Mustafa0801/LFR-thirdspace/CAD files/Fused Motor.FCStd

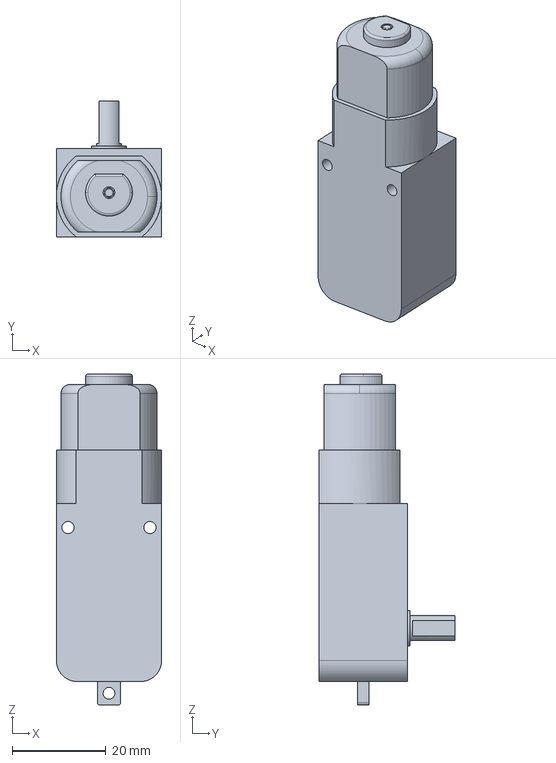
[picture p14: CAD file, 2026-09-21]
CAD files/Fused Motor.FCStd
22.5 x 29.0 x 70.7 mm
