Mustafa0801/LFR-thirdspace/final ship/chassis build current.FCStd

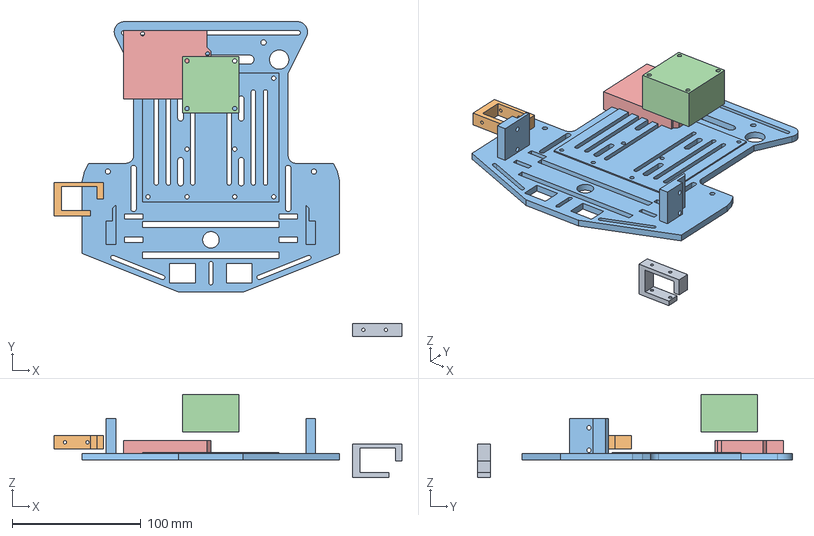
[picture p15: CAD file, 2026-10-05]
final ship/chassis build current.FCStd
270.1 x 244.4 x 64.4 mm
Bracket1
Bracket2
Base Chassis
L298n
Arduino
L298n001
