Mustafa0801/LFR-thirdspace/CAD files/Assorted Assets (Copy 3).FCStd

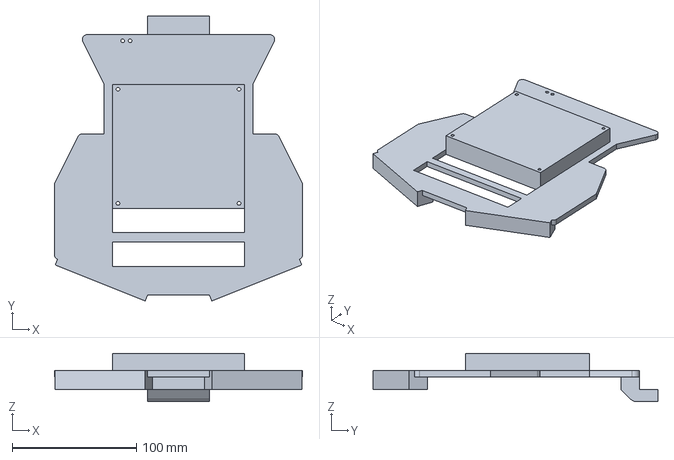
[picture p16: CAD file, 2026-09-21]
CAD files/Assorted Assets (Copy 3).FCStd
200.0 x 229.6 x 39.0 mm
