Mustafa0801/LFR-thirdspace/final ship/chassis build october 3 first space-saving cut.FCStd

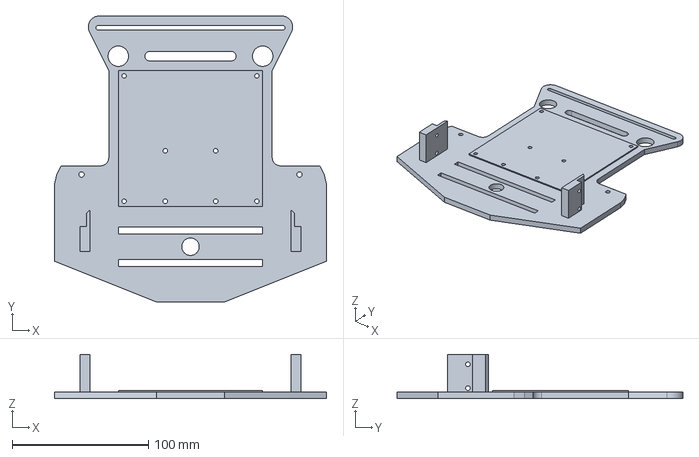
[picture p17: CAD file, 2026-10-05]
final ship/chassis build october 3 first space-saving cut.FCStd
200.0 x 210.0 x 32.5 mm
