Mustafa0801/LFR-thirdspace/CAD files/mule.FCStd

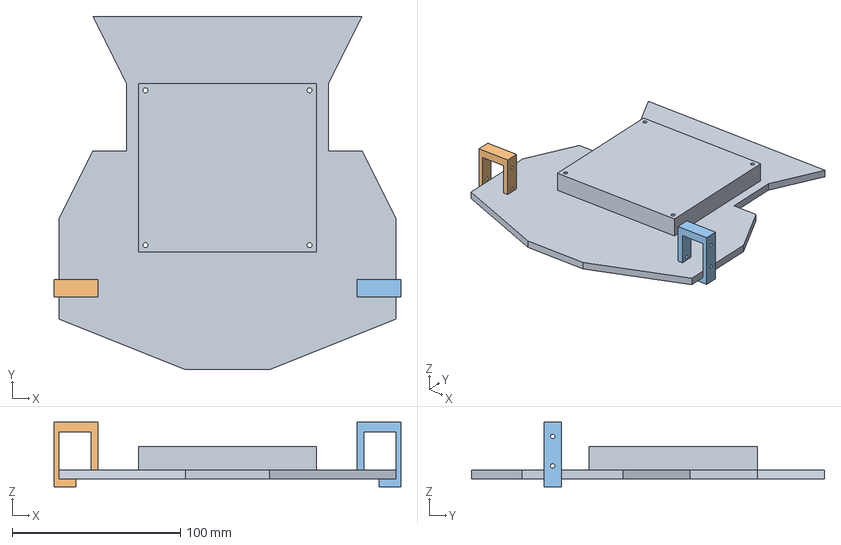
[picture p18: CAD file, 2026-09-21]
CAD files/mule.FCStd
206.2 x 210.0 x 38.5 mm
Base Chassis
Bracket2
Bracket1
