Mustafa0801/LFR-thirdspace/final ship/chassis build october 3 with proper sensor mount and hole for cables.FCStd

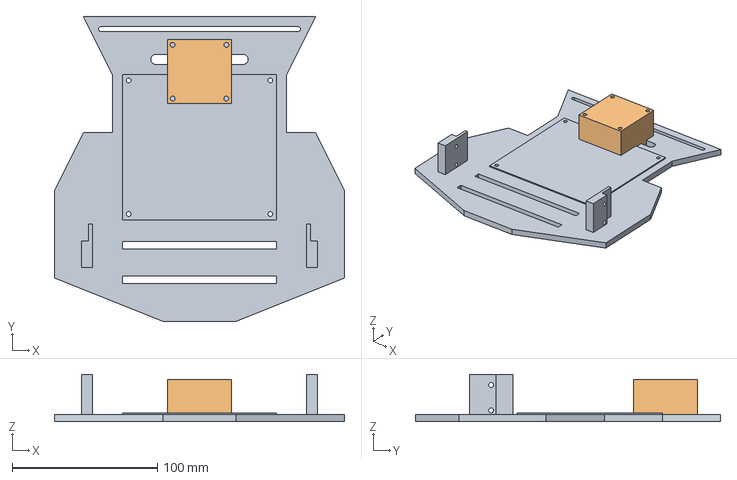
[picture p19: CAD file, 2026-10-05]
final ship/chassis build october 3 with proper sensor mount and hole for cables.FCStd
200.0 x 210.0 x 32.5 mm
Base Chassis
L298n
