Mustafa0801/LFR-thirdspace/CAD files/Assorted Assets (Copy).FCStd

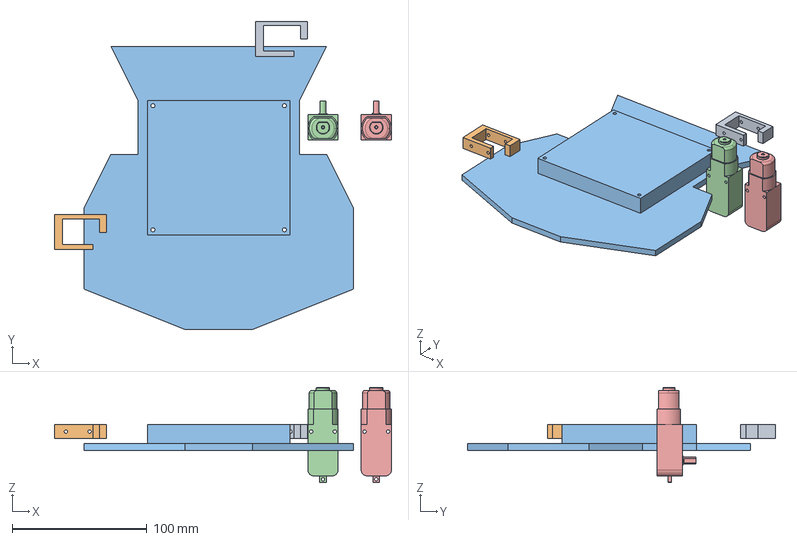
[picture p20: CAD file, 2026-09-21]
CAD files/Assorted Assets (Copy).FCStd
250.0 x 228.5 x 70.7 mm
Bracket1
Bracket2
Base Chassis
Motor fused1
MotorFused2
