Mustafa0801/LFR-thirdspace/CAD files/sensor hanging mounting bracket.FCStd

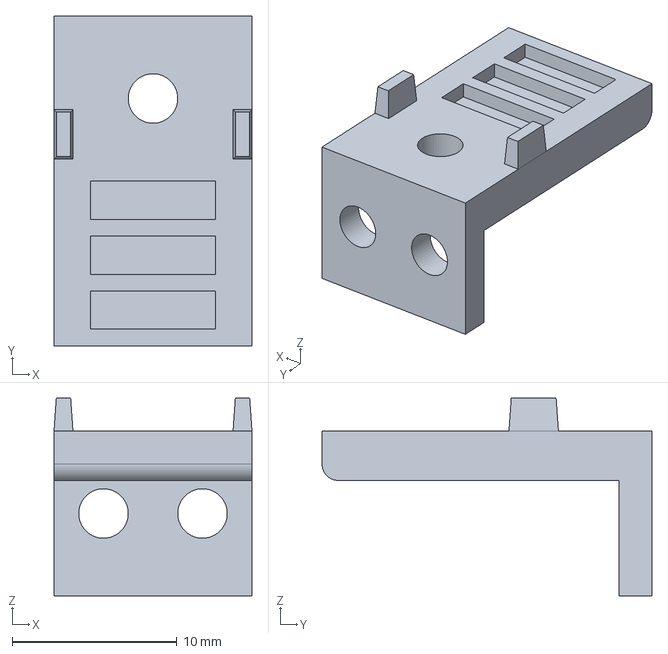
[picture p21: CAD file, 2026-09-21]
CAD files/sensor hanging mounting bracket.FCStd
12.0 x 20.0 x 12.0 mm
