Mustafa0801/LFR-thirdspace/CAD files/fusion1.FCStd

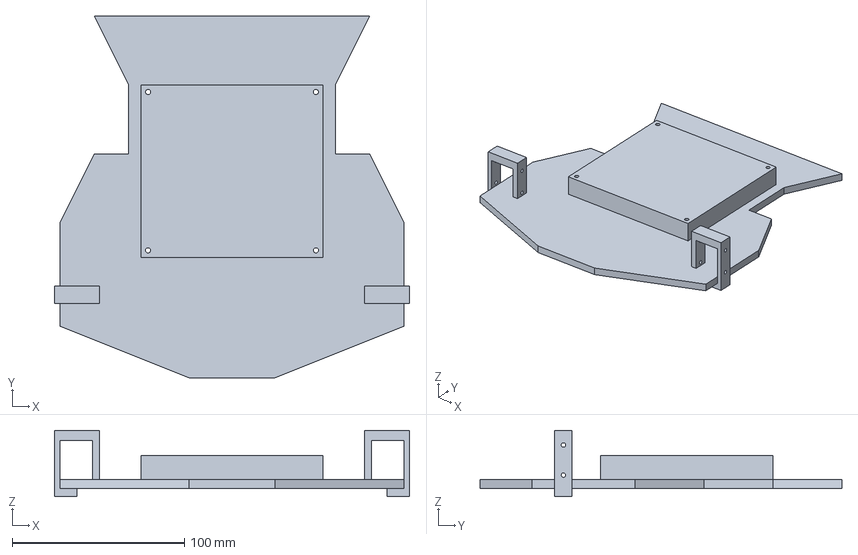
[picture p22: CAD file, 2026-09-21]
CAD files/fusion1.FCStd
206.2 x 210.0 x 38.5 mm
