Mustafa0801/LFR-thirdspace/CAD files/Assorted fusion.FCStd

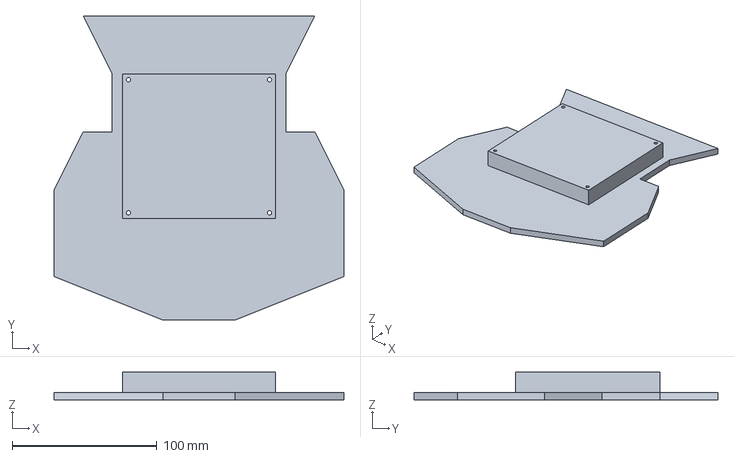
[picture p23: CAD file, 2026-09-21]
CAD files/Assorted fusion.FCStd
200.0 x 210.0 x 19.3 mm
