Mustafa0801/LFR-thirdspace/Arduino Code/other-ideas/speed-adjustment.ino

//  TEST/IDEA FOR HOW SPEED COULD AUTO ADJUST (FOR SHARP TURNS AND STUFF)

//  The code involves checking if a sensor has remained 0 consecutively, 
//  if this sensor is one of the left or right ones then that means a sharp turn is there so robot should slow down to allow it to follow the line properly
//  otherwise if it is the middle one we can deduce that it is following a straight line so it can speed up
// number of consecutive readings would need to be adjusted according to tests

int speed = 150;  // normal speed of car
int linePos;

int countL2 = 0;
int countL1 = 0;
int countM = 0;  // counts how many times each sensor has had value 0 consecutively
int countR1 = 0;
int countR2 = 0;
int consecutive = 2;  // this variable stores the number of consecutive times reading should be same for the robot to change speed (stored in variable to easily change later after tests) 

void setup() {
  // pin modes of sensors and motors here
  Serial.begin(9600);
}

void loop() {
  // ReadSensors function here which will return value for linePos
  
    // PLACEHOLDER: for now using random numbers for linePos
  int zeroChance = random(0,3);  // 33.33% chance the position is 0, this could more accurately represent how our readings probably will actually be with the full robot built 
  if (zeroChance == 0){          
    linePos = 0;
  }
  else{
    linePos = 2*(random(-2,3));  // since just using one random generator will have equal chance for each number
  }

  Serial.print(String(linePos)+"  ");

  switch (linePos){
    case -4:
      // turn left on point function 
      countL2 = countL2 + 1;  // increments counter for left most sensor
      countR2 = countR1 = countM = countL1 = 0;   // sets other counters to zero (since this means the other sensors havent had a consecutive same value)
      break;
    case -2:
      // move left function here
      countL1 = countL1 + 1;
      countR2 = countR1 = countM = countL2 = 0;
      break;
    case 0:
      // move forward function here
      countM = countM + 1;
      countR2 = countR1 = countL1 = countL2 = 0;
      break;
    case 2:
      // move right function here
      countR1 = countR1 + 1;
      countR2 = countM = countL1 = countL2 = 0;
      break;
    case 4:
      // turn right on point function here
      countR2 = countR2 + 1;
      countR1 = countM = countL1 = countL2 = 0;
      break;
  }

  if (countL2 == consecutive){
    if (speed>30){    // only decreases speed if above lower threshold of 30
      speed = speed*0.75;  // decreases speed by 25% 
      countL2 = 0;  // resets counter
      if (speed<30){  // if speed goes below 30 it is reset to 30
        speed = 30;
      }
      Serial.print("speed decreased to: "+String(speed));
    }
  } 
  else if (countL1 == consecutive){
    if (speed>50){     // only decreases speed if above 50
      speed = speed*0.9;  // decreases speed by 10%
      countL1 = 0;
      if (speed<50){  // if speed goes below 50 it is reset to 50
        speed = 50;
      }
      Serial.print("speed decreased to: "+String(speed));
    } 
  }
  else if (countM == consecutive){
    if (speed<150){   // only increases if speed below maximum threshold of 150
      speed = speed + 25;  // increases speed if robot is following a long straight line 
      countM = 0; 
      if (speed>150){  // ensures speed never goes above 150
        speed = 150;
      }
      Serial.print("speed increased to: "+String(speed));
    }
    
  }
  else if (countR1 == consecutive){
    if (speed>50){
      speed = speed*0.9;
      countR1 = 0;
      if (speed<50){
        speed = 50;
      }
      Serial.print("speed decreased to: "+String(speed));
    }
  }
  else if (countR2 == consecutive){
    if (speed>30){
      speed = speed*0.75;
      countR2 = 0;
      if (speed<30){
        speed = 30;
      }
      Serial.print("speed decreased to: "+String(speed));
    }
  }

  Serial.println(); // goes to next line
}
